atarnowsky/TickTockTubeClock/firmware/src/hw_map.cpp

#include "hw_map.h"


void Pins::setup() {
    IO::configure<INPUT_PULLUP>(
        I2C::SDA, I2C::SCL // There are already 10K pullup on board, but internals won't make it worse
    );

    IO::configure<OUTPUT>(
        Speaker, Light,
        Shift::Data, Shift::Clock, Shift::Latch,
        Anode::MuxA, Anode::MuxB
    );
}
